ccblaisdell/dimetrodon/outlines/preview.dxf

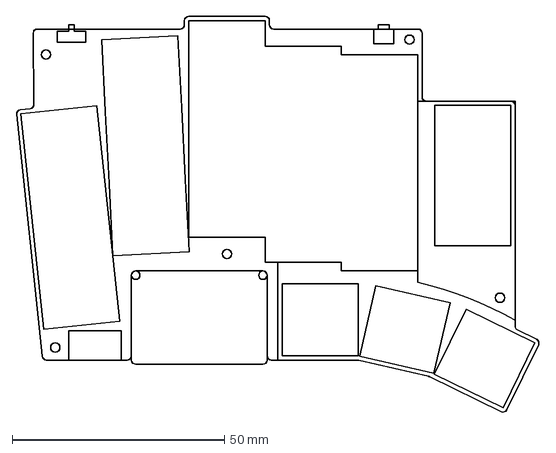
[picture p15: CAD file, 2024-12-04]
outlines/preview.dxf
123.3 x 93.4 mm
