ccblaisdell/dimetrodon/outlines/left_board.dxf

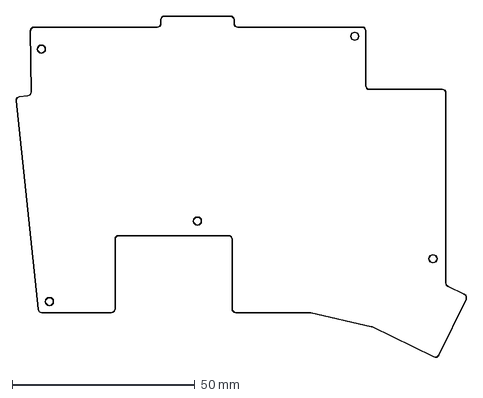
[picture p16: CAD file, 2024-12-04]
outlines/left_board.dxf
123.3 x 93.4 mm
