ccblaisdell/dimetrodon/outlines/base.dxf

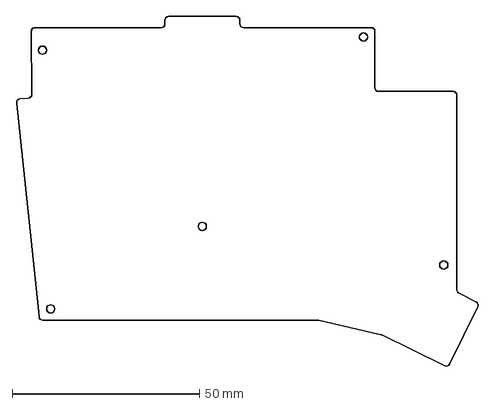
[picture p17: CAD file, 2024-12-04]
outlines/base.dxf
123.3 x 93.4 mm
