ccblaisdell/dimetrodon/outlines/keywell.dxf

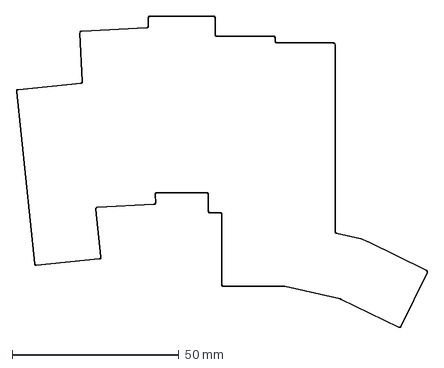
[picture p18: CAD file, 2024-11-29]
outlines/keywell.dxf
123.4 x 93.5 mm
